M0LTE/pi-transceiver/electronics/bits'n_bobs/Modular_PA Controller/HF PA Radio Interface/RaspberryPi_Pico/README.txt

**A comprehensive KiCad Library for the Raspberry Pi Pico** 🥧
==============================================================

### Providing footprints, symbols, & models for the module's various forms & implementations

> *This git submodule only contains the finished library.  For source files and commit history, see [Ki-Lime Pi Pico][URL-Repository]*.

***Features***
==============

- **KiCad 8.0 support** *(For KiCad 7.0 support, checkout tag `1.1.0`)*
- **Schematics with alternate pin definitions** to select more specific behaviours for each GPIO, as well as specify power directionality
- **Generic and specific footprints** for the Pico and Pico W
  - Through-hole and surface-mount footprints with and without mounting holes
  - Hand-solderable test points (ie. USB signals) in footprints with underside castellations
  - Optional pin labels as an add-on footprint
  - Optional keepout zone for 2.4 GHz RF on shared footprints
  - Ability to add individual schematic symbols for sockets, and a virtual Pico for the BOM and rendering
- **Diverse 3D models** for surface-mount, through-hole, and socketed forms of the Pico, Pico H, Pico W, and Pico WH using photorealistic materials
- Majority adherence to the [KiCad Library Conventions][URL-KLC] version 3.0.41

***How do I use this library as a git submodule?***
===================================================

> *If you're looking to use this library without submodules, you probably want the source repository [Ki-Lime Pi Pico][URL-Repository].*

- Ensure you are running KiCad 7.0 or later
- Identify the path where you want this library to live in your project  
  *(below, I will use `<GIT-ROOT>/pcb/project-libraries/RaspberryPi_Pico`)*
- From within your git repository, call:
  - `git submodule add --name ki-lime-pi-pico https://github.com/recursivenomad/ki-lime-pi-to-go.git pcb/project-libraries/RaspberryPi_Pico`  
    *(Adjusting these parameters as you see fit)*
  - `cd pcb/project-libraries/RaspberryPi_Pico`
  - `git checkout 2.0.0` *(For KiCad 7.0 support, checkout `1.1.0` instead)*
- Open the relevant KiCad project
- Select `Preferences > Manage Footprint Libraries...`
- Select the `Project Specific Libraries` tab
- Click the folder icon in the lower left to `Add Existing`
- Navigate to and select `.../RaspberryPi_Pico/Module_RaspberryPi_Pico.pretty/`
- Click `OK`
- Select `Preferences > Manage Symbol Libraries...`
- Select the `Project Specific Libraries` tab
- Click the folder icon in the lower left to `Add existing library to table`
- Navigate to and select `.../RaspberryPi_Pico/MCU_Module_RaspberryPi_Pico.kicad_sym`
- Click `OK`

To use, simply add a symbol to your schematic as you would any other; symbols should be located under the section `MCU_Module_RaspberryPi_Pico`, and footprints under `Module_RaspberryPi_Pico`.

**You're all set to design exciting new circuit boards using the Raspberry Pi Pico! 🎉**

***Further reading***
=====================

*Further reading available in the [source repository][URL-Repository].*

***License / Access***
======================

This work is made freely available under the [*MIT-0*][URL-MIT-0] license, rendered in [`LICENSE.txt`](./LICENSE.txt).  
Although attribution is not required, sharing when you've made something with my work is really cool ❤✨

*No additional/conflicting permissions were present in this repository at the time of release.*

----------------------

*Repository: <https://gitlab.com/recursivenomad/ki-lime-pi-pico/>*  
*Releases: <https://gitlab.com/recursivenomad/ki-lime-pi-pico/-/releases/>*  
*Submodule: <https://github.com/recursivenomad/ki-lime-pi-to-go/>*  
*Contact: <recursivenomad@protonmail.com>*

----------------------

### Donations:

*Accepted, but not expected*

> Online payment: <https://donate.stripe.com/dR6dSU1PueevgKY4gs>

> Monero (XMR): `8Bhyeo232EVDiK7aRSzHGRC28RZ1H6FL55V6CVyCVtxdDRQXHk8btPU8Wr5G8K3AWgaK19JfYbshKfHWqc177jwtCtCSaz1`

> Ether (ETH): `0xD1b824f2Ec3D609e816B04A301124129602A5238`

> Bitcoin (BTC): `bc1qadq5kyuuc7etgu5ywlygnaepqhzgc2u7gxkze2`

[URL-MIT-0]: <https://opensource.org/license/mit-0/>

[URL-Repository]: <https://gitlab.com/recursivenomad/ki-lime-pi-pico/>

[URL-KiCad-Forums-cdwilson]: <https://forum.kicad.info/t/21104>
[URL-KiCad-Forums-mgyger]: <https://forum.kicad.info/t/35844/12>
[URL-KLC]: <https://klc.kicad.org/>
[URL-Official-Example]: <https://datasheets.raspberrypi.com/rp2040/hardware-design-with-rp2040.pdf#page=15>
