M0LTE/pi-transceiver/electronics/PSU Board/Schematic.png

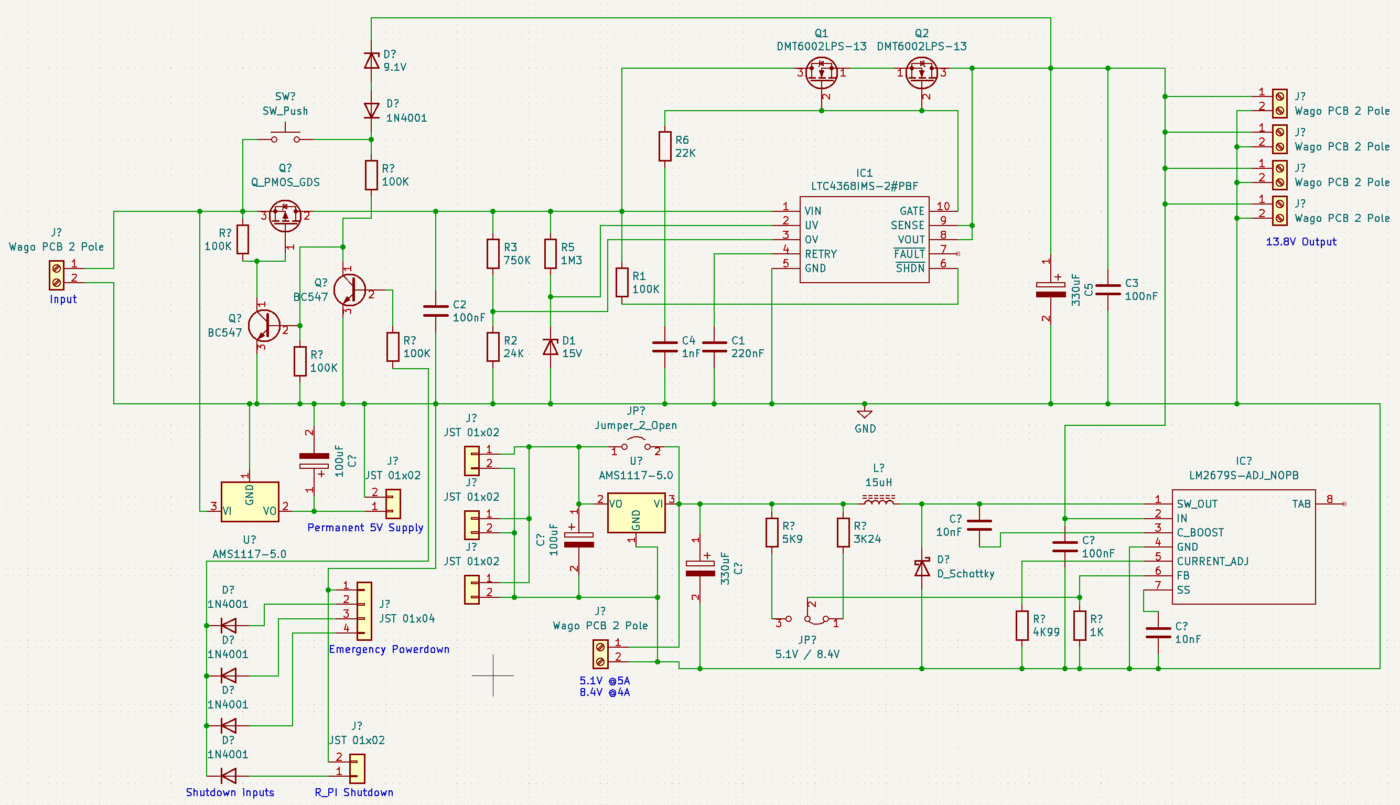
electronics/PSU Board/Schematic.png
