M0LTE/pi-transceiver/electronics/PSU Board/WEBENCH LM2679 Efficiency.png

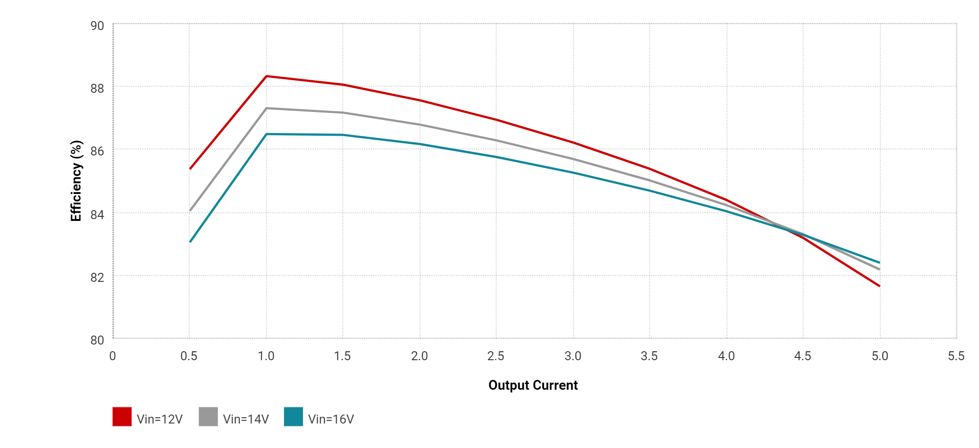
electronics/PSU Board/WEBENCH LM2679 Efficiency.png
