M0LTE/pi-transceiver/electronics/PSU Board/WEBENCH LM2679 Schematic.png

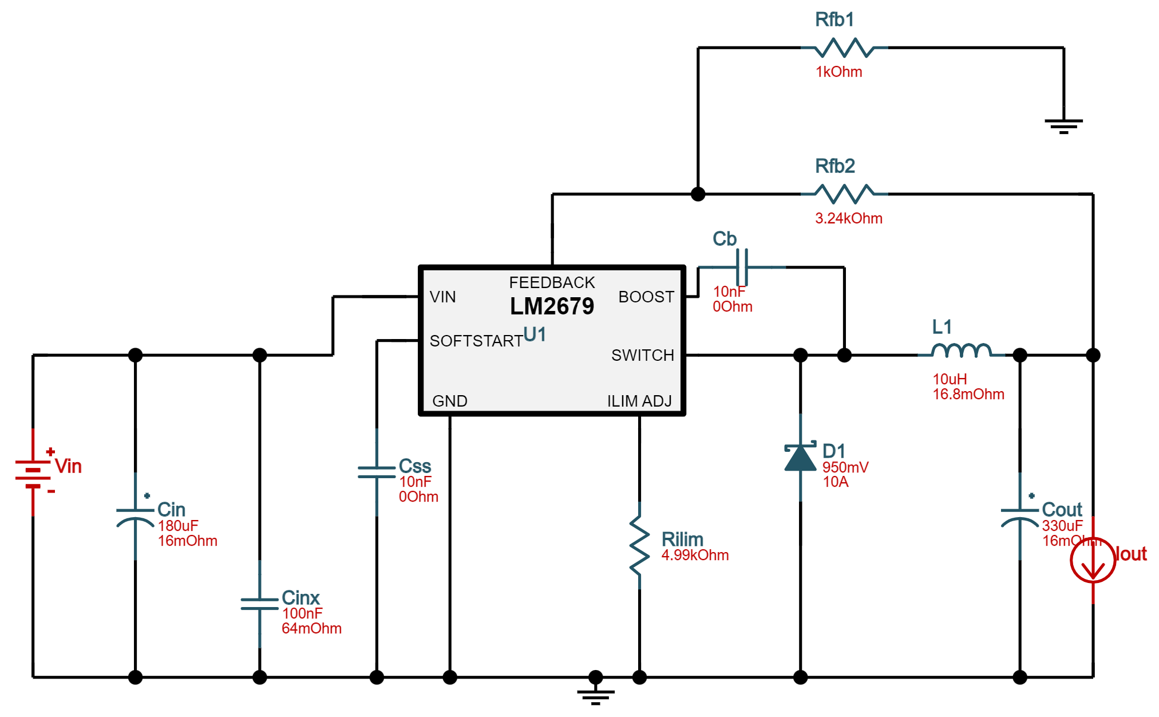
electronics/PSU Board/WEBENCH LM2679 Schematic.png
