M0LTE/pi-transceiver/electronics/receiver/RXLNA.jpg

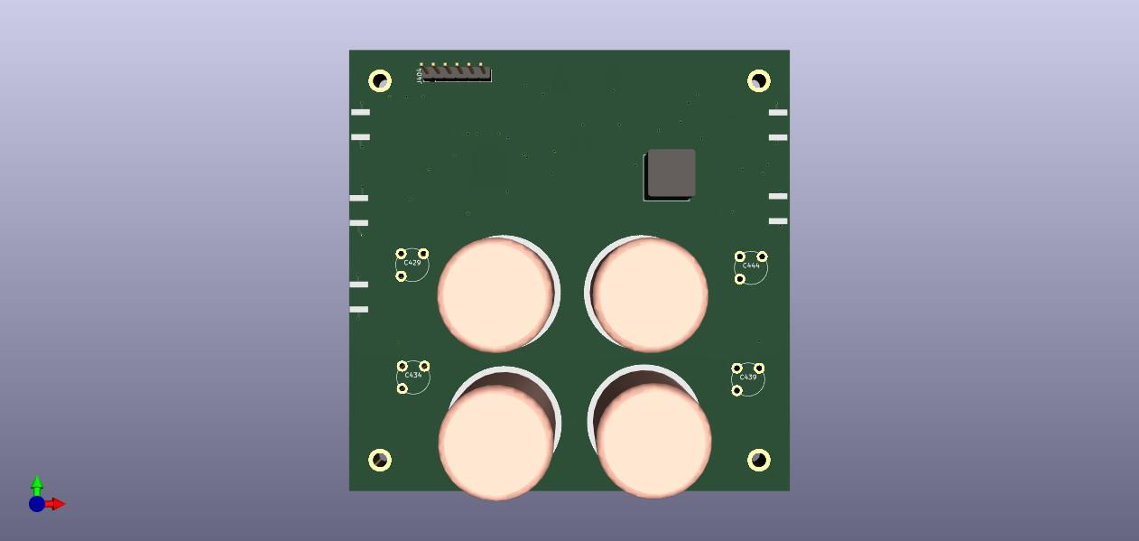
electronics/receiver/RXLNA.jpg
