M0LTE/pi-transceiver/electronics/PA_Board_V2/JST/JST_PH/JST - PH - SMD - Right - 1.25mm/JST - PH - SMD (R) - 13Pin - 2.00mm.stp

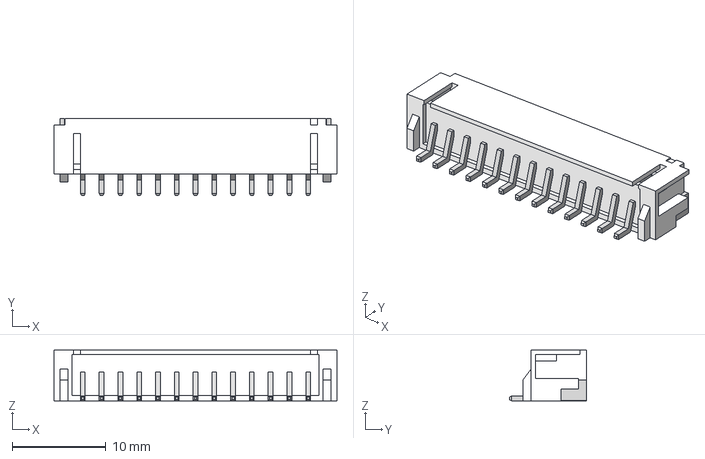
[picture p19: CAD file, 2022-10-31]
electronics/PA_Board_V2/JST/JST_PH/JST - PH - SMD - Right - 1.25mm/JST - PH - SMD (R) - 13Pin - 2.00mm.stp
30.1 x 8.26 x 5.38 mm
