M0LTE/pi-transceiver/electronics/bits'n_bobs/Modular_PA Controller/PA_Power_V1/RLab Keyboard/3D_Models/3214G.stp

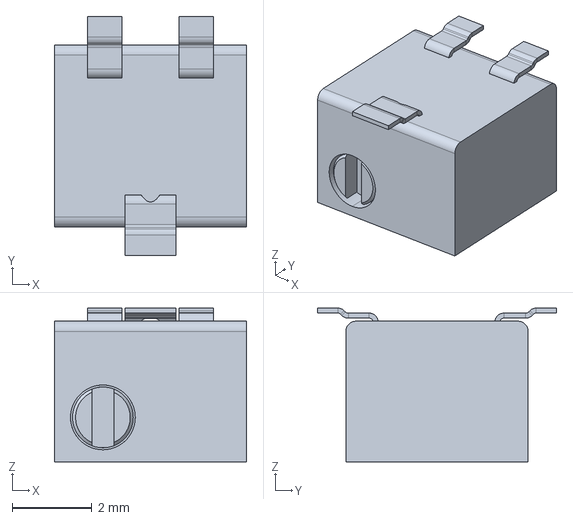
[picture p25: CAD file, 2024-11-24]
electronics/bits'n_bobs/Modular_PA Controller/PA_Power_V1/RLab Keyboard/3D_Models/3214G.stp
4.83 x 5.99 x 3.86 mm
