M0LTE/pi-transceiver/electronics/PA_Board_V2/3D/SAMTEC_RF174-01SPX-06BJX-XXX-S-1.STEP

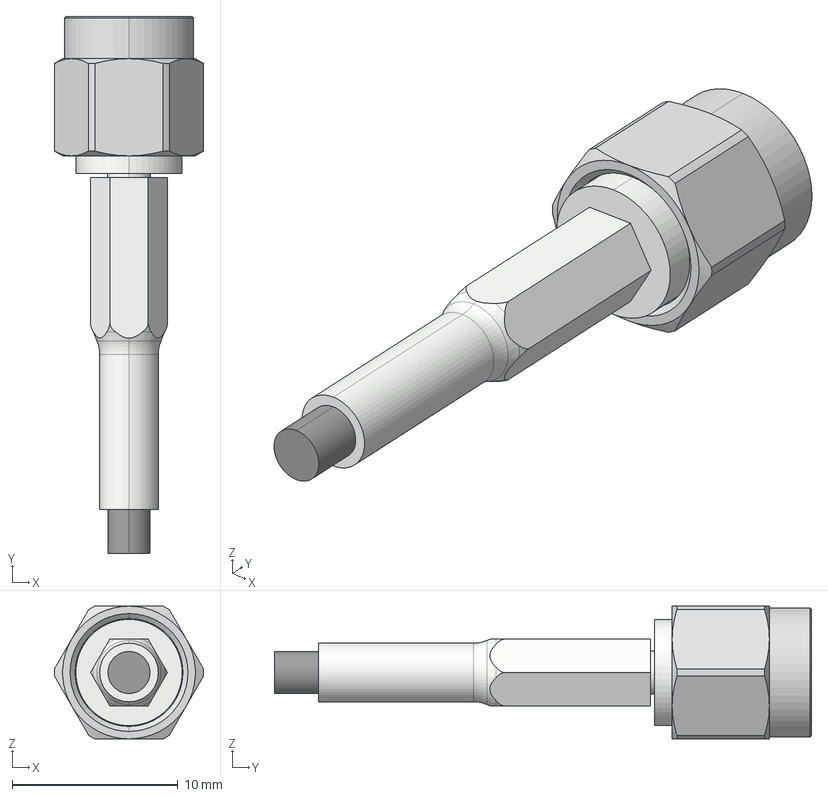
[picture p26: CAD file, 2022-10-31]
electronics/PA_Board_V2/3D/SAMTEC_RF174-01SPX-06BJX-XXX-S-1.STEP
9.00 x 32.4 x 8.00 mm
