M0LTE/pi-transceiver/electronics/PA_Board_V2/JST/JST_PH/JST - PH - Thru - Vertical - 2.00mm/JST - PH - Thru (V) - 16Pin - 2.00mm.stp

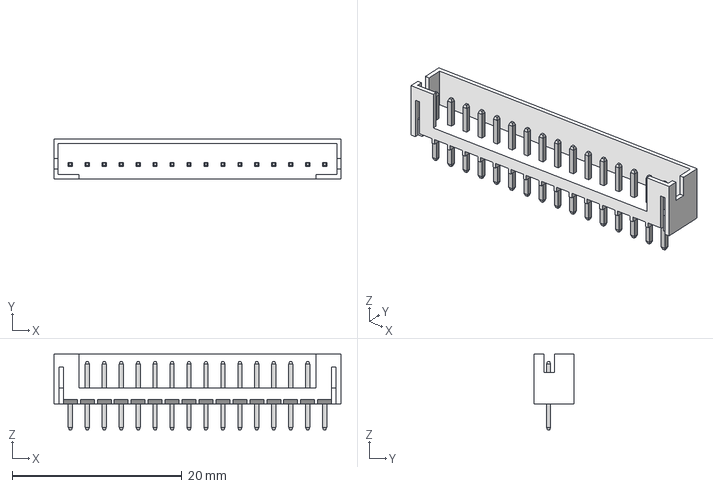
[picture p28: CAD file, 2022-10-31]
electronics/PA_Board_V2/JST/JST_PH/JST - PH - Thru - Vertical - 2.00mm/JST - PH - Thru (V) - 16Pin - 2.00mm.stp
33.9 x 4.67 x 8.94 mm
