M0LTE/pi-transceiver/electronics/PA_Board_V2/JST/JST_SH/SHR-xxV-S/SHR-10V-S.STEP

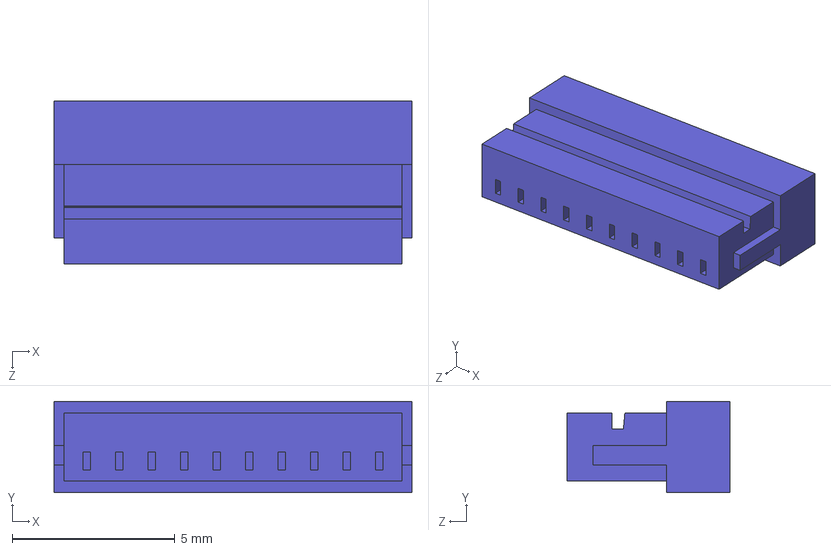
[picture p31: CAD file, 2022-10-31]
electronics/PA_Board_V2/JST/JST_SH/SHR-xxV-S/SHR-10V-S.STEP
11.0 x 2.80 x 5.00 mm
