M0LTE/pi-transceiver/electronics/bits'n_bobs/Modular_PA Controller/PA_Power_V1/RLab Keyboard/3D_Models/PJ311D_WPos.STEP

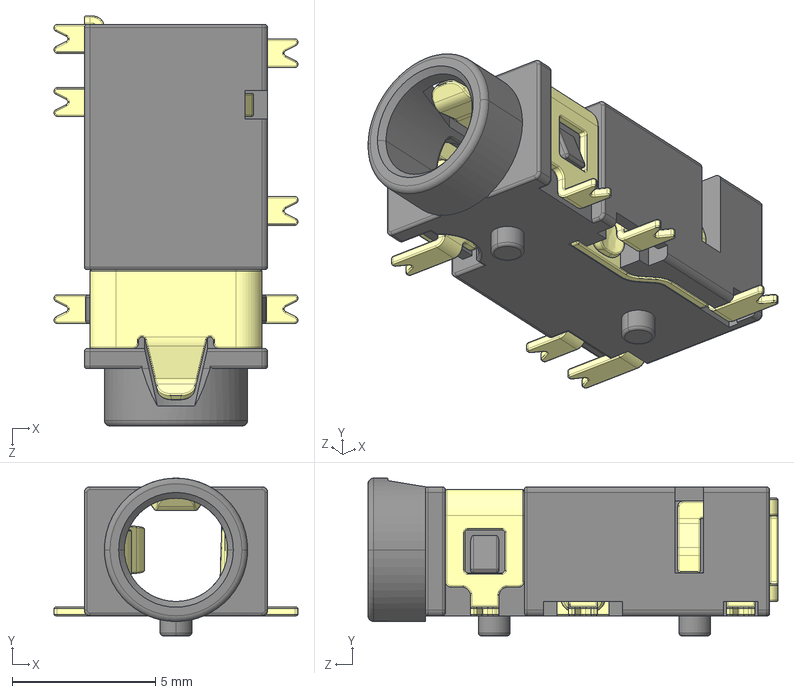
[picture p33: CAD file, 2024-11-24]
electronics/bits'n_bobs/Modular_PA Controller/PA_Power_V1/RLab Keyboard/3D_Models/PJ311D_WPos.STEP
8.50 x 5.50 x 14.3 mm
001^PJ311D_WPos
002^PJ311D_WPos
003^PJ311D_WPos
004^PJ311D_WPos
005^PJ311D_WPos
006^PJ311D_WPos
007^PJ311D_WPos
