M0LTE/pi-transceiver/electronics/PA_Board_V2/3D/Power Pole v1.step

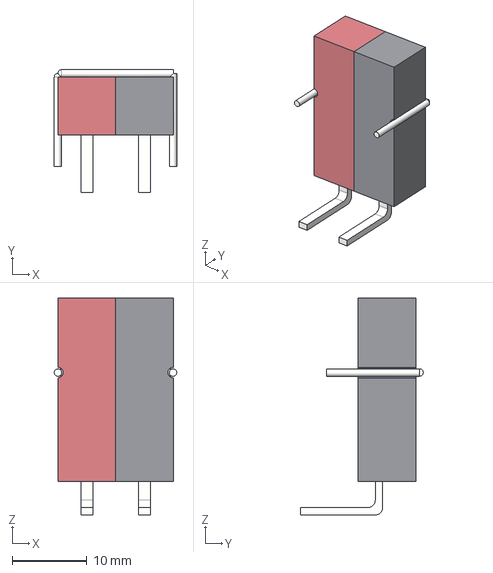
[picture p34: CAD file, 2022-10-31]
electronics/PA_Board_V2/3D/Power Pole v1.step
16.4 x 16.4 x 29.1 mm
