M0LTE/pi-transceiver/electronics/bits'n_bobs/Modular_PA Controller/PA_Power_V1/RLab Keyboard/3D_Models/1.3 TFT IPS.stp

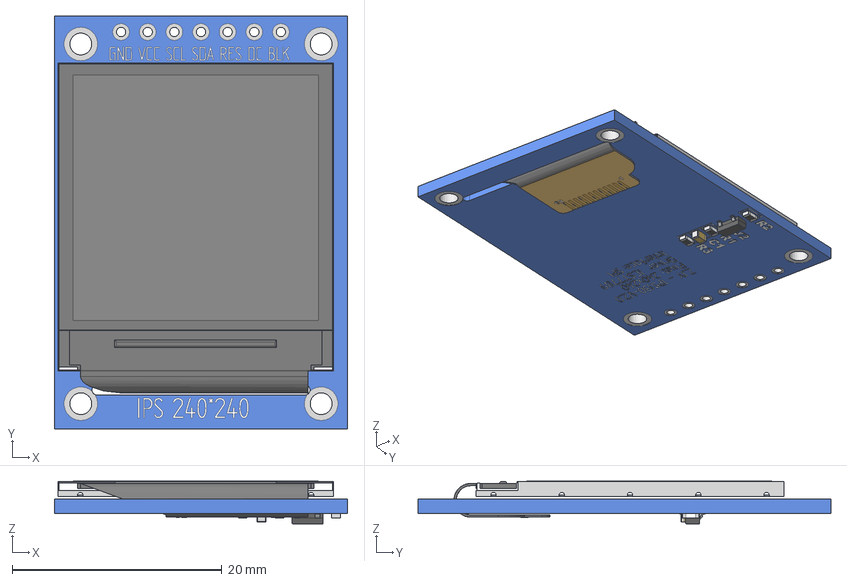
[picture p41: CAD file, 2024-11-24]
electronics/bits'n_bobs/Modular_PA Controller/PA_Power_V1/RLab Keyboard/3D_Models/1.3 TFT IPS.stp
27.9 x 39.4 x 4.06 mm
1.3 TFT IPS - Board
1.3 TFT IPS - Flush Reverse Mount
0603 Resistor x 3
0603 Capacitor
SOT-23
