M0LTE/pi-transceiver/electronics/PA_Board_V2/3D/PA_module_copper .step

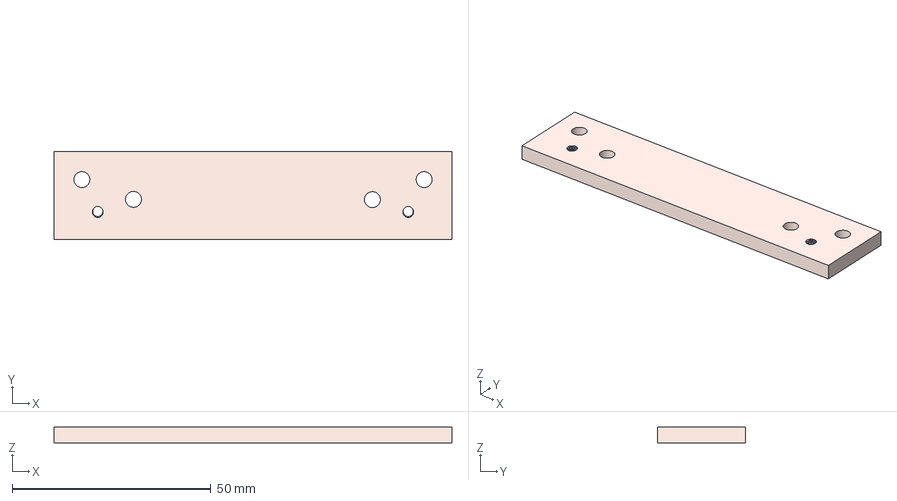
[picture p48: CAD file, 2022-10-31]
electronics/PA_Board_V2/3D/PA_module_copper .step
100.0 x 22.0 x 4.00 mm
