M0LTE/pi-transceiver/electronics/PA_Board_V2/JST/JST_SH/SHR-xxV-S/SHR-08V-S.STEP

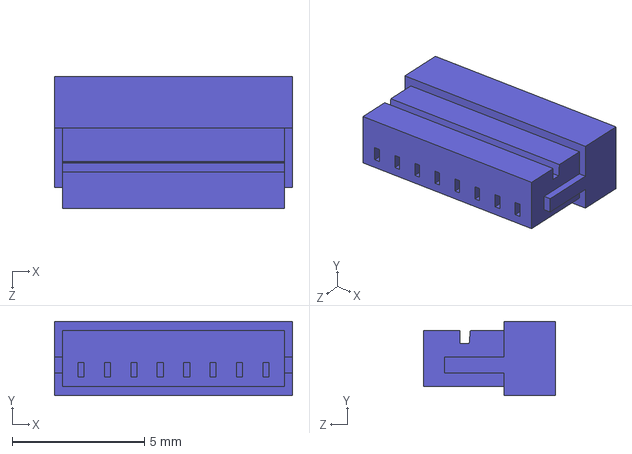
[picture p53: CAD file, 2022-10-31]
electronics/PA_Board_V2/JST/JST_SH/SHR-xxV-S/SHR-08V-S.STEP
9.00 x 2.80 x 5.00 mm
