M0LTE/pi-transceiver/electronics/PA_Board_V2/3D/SAMTEC_SMA-J-P-H-ST-EM1.STEP

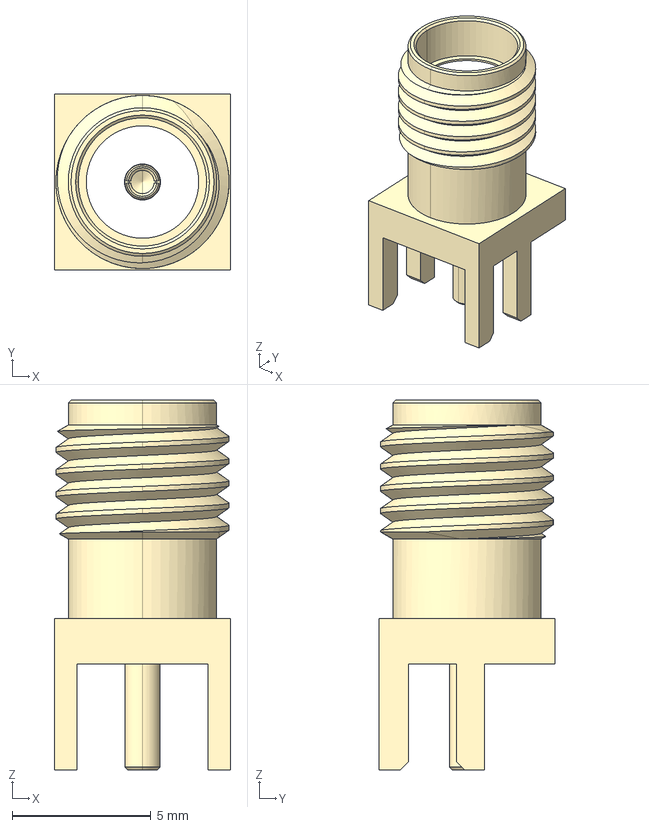
[picture p55: CAD file, 2022-10-31]
electronics/PA_Board_V2/3D/SAMTEC_SMA-J-P-H-ST-EM1.STEP
6.35 x 6.35 x 13.3 mm
