M0LTE/pi-transceiver/electronics/PA_Board_V2/3D/RF_PA_module.step

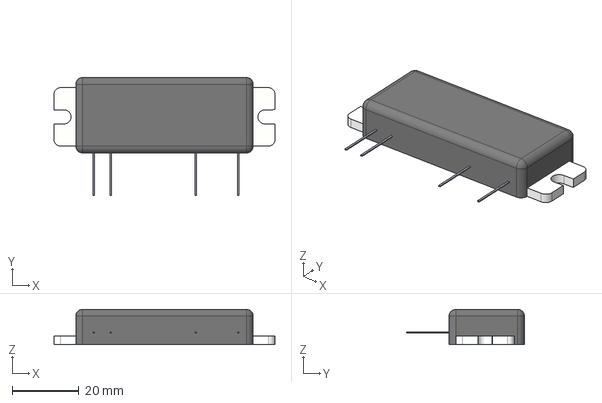
[picture p62: CAD file, 2022-10-31]
electronics/PA_Board_V2/3D/RF_PA_module.step
66.0 x 35.2 x 10.5 mm
