M0LTE/pi-transceiver/electronics/PA_Board_V2/JST/JST_SH/BMxxB-SRSR-TB/BM08B-SRSS-TB.STEP

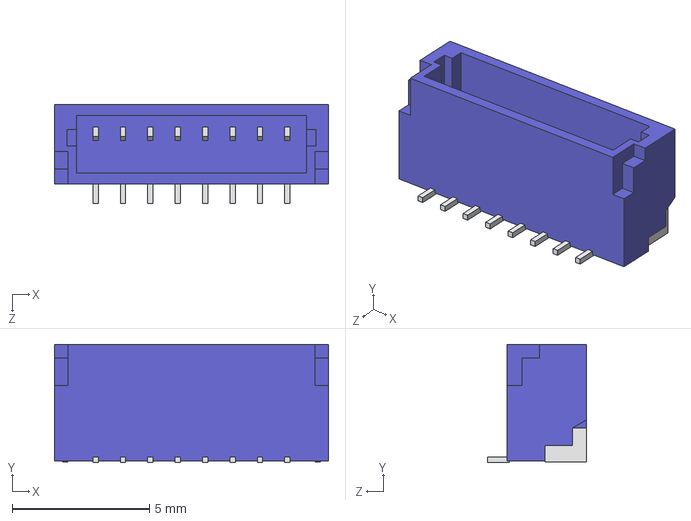
[picture p65: CAD file, 2022-10-31]
electronics/PA_Board_V2/JST/JST_SH/BMxxB-SRSR-TB/BM08B-SRSS-TB.STEP
10.0 x 4.32 x 3.60 mm
