M0LTE/pi-transceiver/electronics/PA_Board_V2/JST/JST_SH/SHR-xxV-S-B/SHR-04V-S-B.STEP

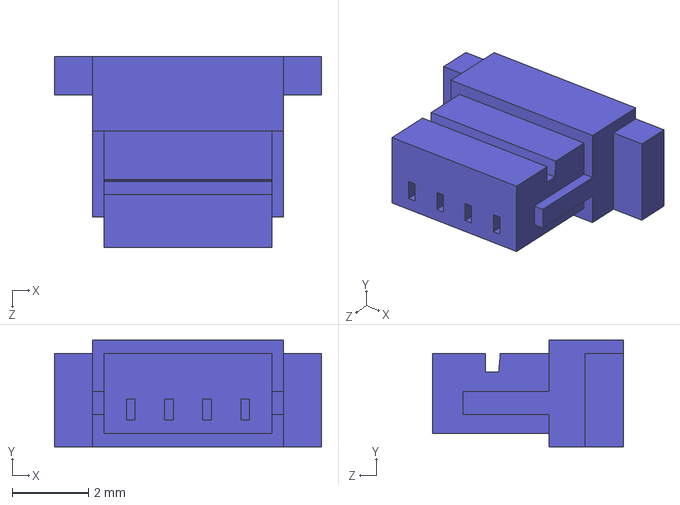
[picture p66: CAD file, 2022-10-31]
electronics/PA_Board_V2/JST/JST_SH/SHR-xxV-S-B/SHR-04V-S-B.STEP
7.00 x 2.80 x 5.00 mm
