M0LTE/pi-transceiver/electronics/PA_Board_V2/JST/JST_SH/SMxxB-SRSS-TB/SM03B-SRSS-TB.STEP

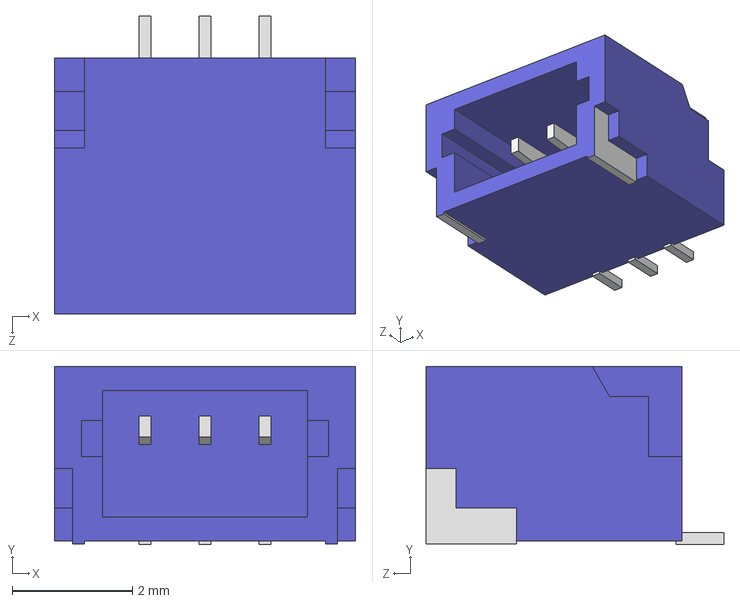
[picture p92: CAD file, 2022-10-31]
electronics/PA_Board_V2/JST/JST_SH/SMxxB-SRSS-TB/SM03B-SRSS-TB.STEP
5.00 x 2.96 x 4.95 mm
