M0LTE/pi-transceiver/electronics/PA_Board_V2/JST/JST_SH/SHR-xxV-S-B/SHR-15V-S-B.STEP

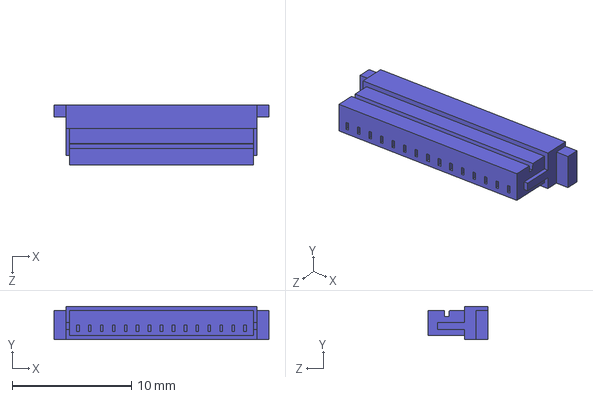
[picture p96: CAD file, 2022-10-31]
electronics/PA_Board_V2/JST/JST_SH/SHR-xxV-S-B/SHR-15V-S-B.STEP
18.0 x 2.80 x 5.00 mm
