M0LTE/pi-transceiver/electronics/PA_Board_V2/JST/JST_SH/BMxxB-SRSR-TB/BM03B-SRSS-TB.STEP

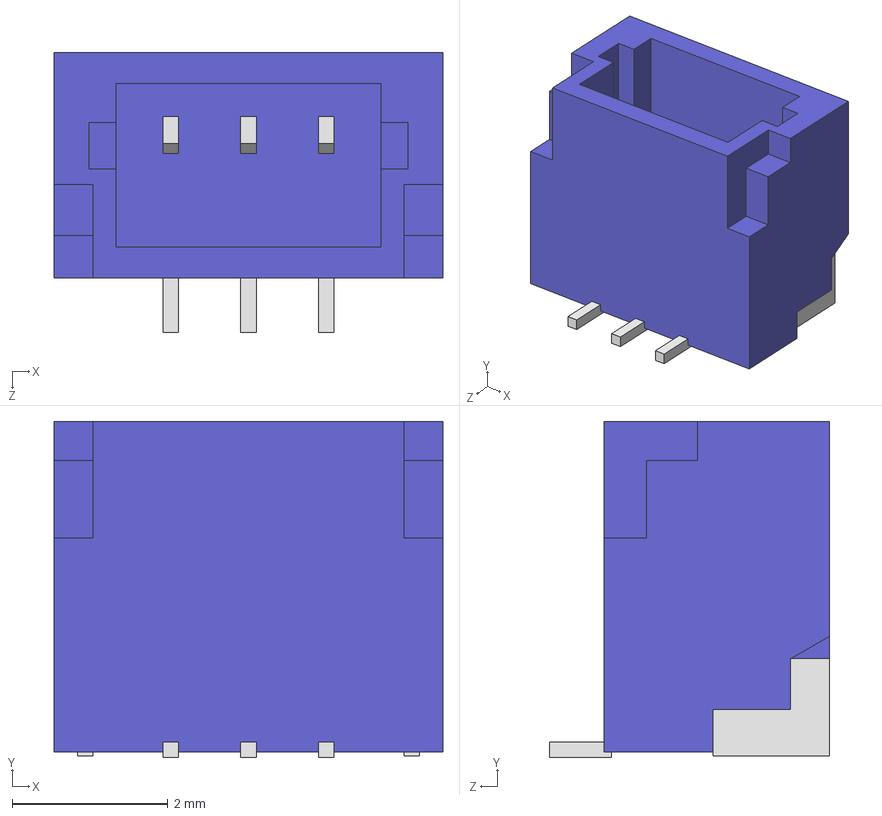
[picture p101: CAD file, 2022-10-31]
electronics/PA_Board_V2/JST/JST_SH/BMxxB-SRSR-TB/BM03B-SRSS-TB.STEP
5.00 x 4.32 x 3.60 mm
