M0LTE/pi-transceiver/electronics/PA_Board_V2/JST/JST_SH/SHR-xxV-S-B/SHR-08V-S-B.STEP

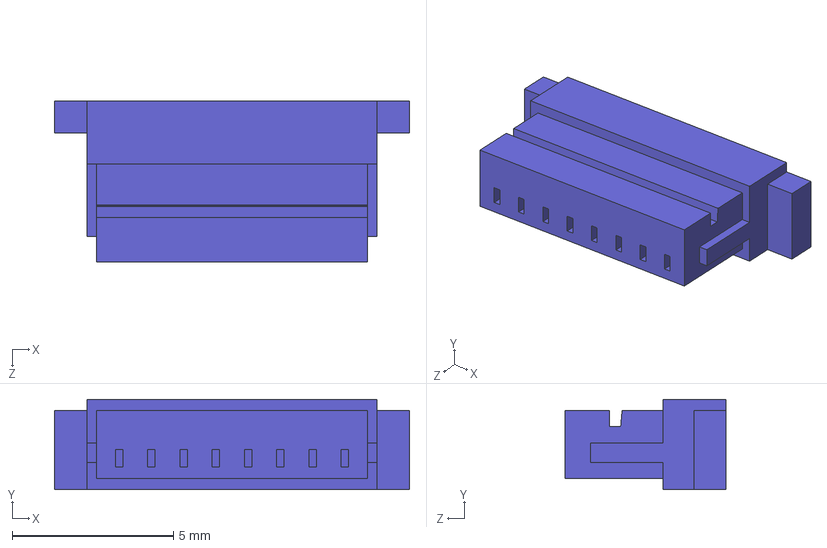
[picture p107: CAD file, 2022-10-31]
electronics/PA_Board_V2/JST/JST_SH/SHR-xxV-S-B/SHR-08V-S-B.STEP
11.0 x 2.80 x 5.00 mm
