M0LTE/pi-transceiver/electronics/bits'n_bobs/Relays/Relay_RF_HF3/Relay_RF_HF3.kicad_pcb

## KiCad design electronics/bits'n_bobs/Relays/Relay_RF_HF3/Relay_RF_HF3.kicad_pcb (2022-03-16)

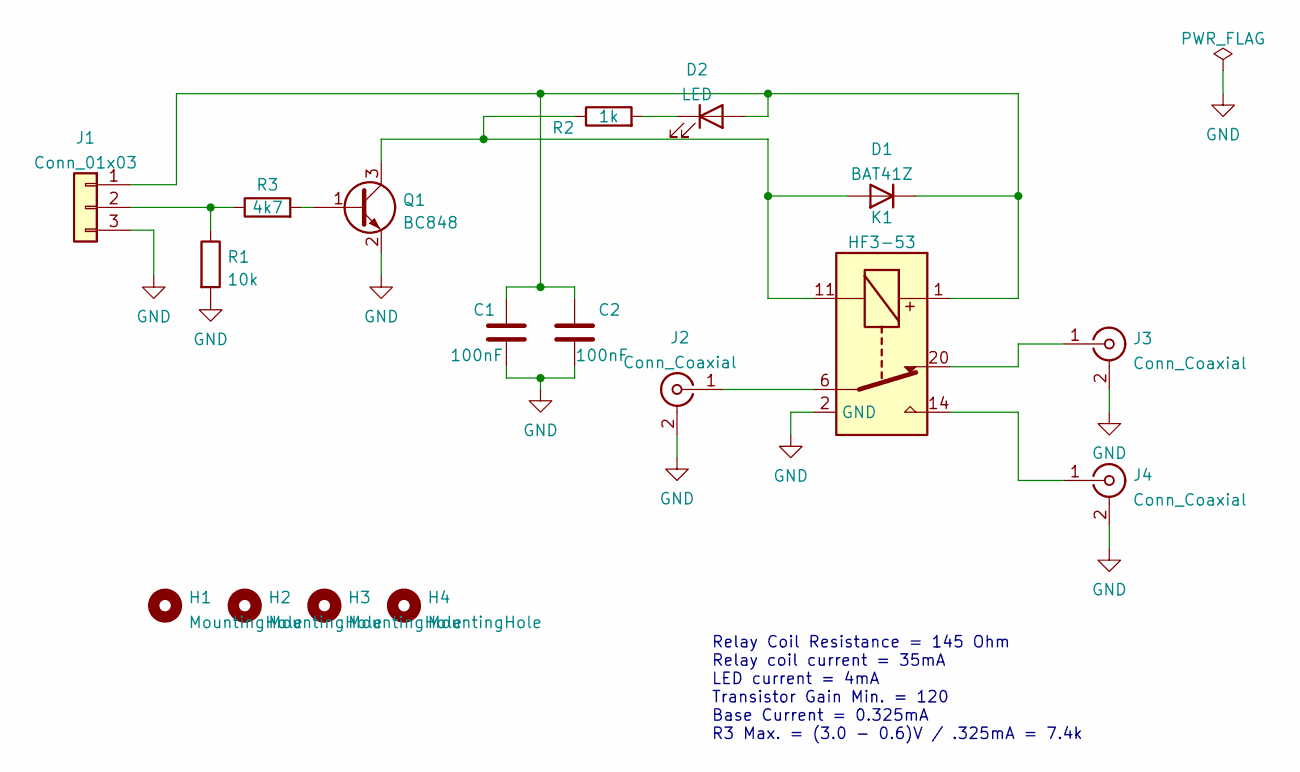
[picture p150: schematic Relay_RF_HF3.kicad_sch]

Parts:
C1, C2: 100nF; C_0603_1608Metric
D1: BAT41Z; D_SOD-123
D2: LED; LED_0603_1608Metric
H1, H2, H3, H4: MountingHole; MountingHole_2.7mm_M2.5_DIN965
J1: Conn_01x03; JST_PH_B3B-PH-SM4-TB_1x03-1MP_P2.00mm_Vertical
J2, J3, J4: Conn_Coaxial; SMA_Samtec_SMA-J-P-X-ST-EM1_EdgeMount
K1: HF3-53; Relay_SPDT_AXICOM_HF3Series_50ohms_Pitch1.27mm
Q1: BC848; SOT-23
R1: 10k; R_0603_1608Metric
R2: 1k; R_0603_1608Metric
R3: 4k7; R_0603_1608Metric

Connections:
GND: C1.2, C2.2, J1.3, J2.2 (Ext), J3.2 (Ext), J4.2 (Ext), K1.2 (GND), K1.5 (GND), K1.7 (GND), K1.10 (GND), K1.12 (GND), K1.13 (GND), K1.15 (GND), K1.17 (GND), K1.19 (GND), K1.21 (GND), K1.22 (GND), Q1.2 (E), R1.2
unnamed: C1.1, C2.1, D1.1 (K), D2.2 (A), J1.1, K1.1
unnamed: D1.2 (A), K1.11, Q1.3 (C), R2.1
unnamed: D2.1 (K), R2.2
unnamed: J1.2, R1.1, R3.1
unnamed: J2.1 (In), K1.6
unnamed: J3.1 (In), K1.20
unnamed: J4.1 (In), K1.14
unnamed: Q1.1 (B), R3.2

Notes on the sheet:
Relay Coil Resistance = 145 Ohm Relay coil current = 35mA LED current = 4mA Transistor Gain Min. = 120 Base Current = 0.325mA R3 Max. = (3.0 - 0.6)V / .325mA = 7.4k

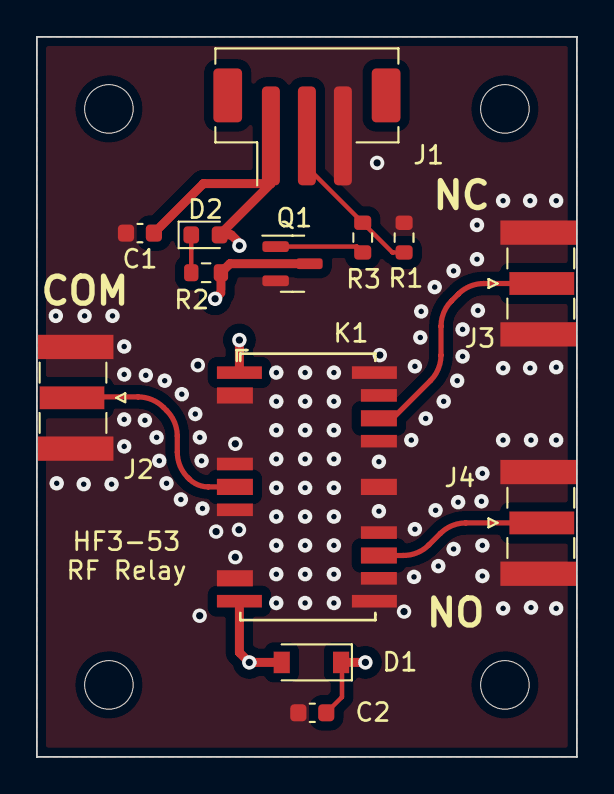
[picture p151: board Relay_RF_HF3.kicad_pcb from above]

Board: 4 copper layers, 30.0 x 40.0 mm, 17 parts (0 on the bottom side), 9 nets.
