M0LTE/pi-transceiver/electronics/bits'n_bobs/Filters/RBP-140+/RBP-140+.kicad_pcb

## KiCad design electronics/bits'n_bobs/Filters/RBP-140+/RBP-140+.kicad_pcb (2022-03-16)

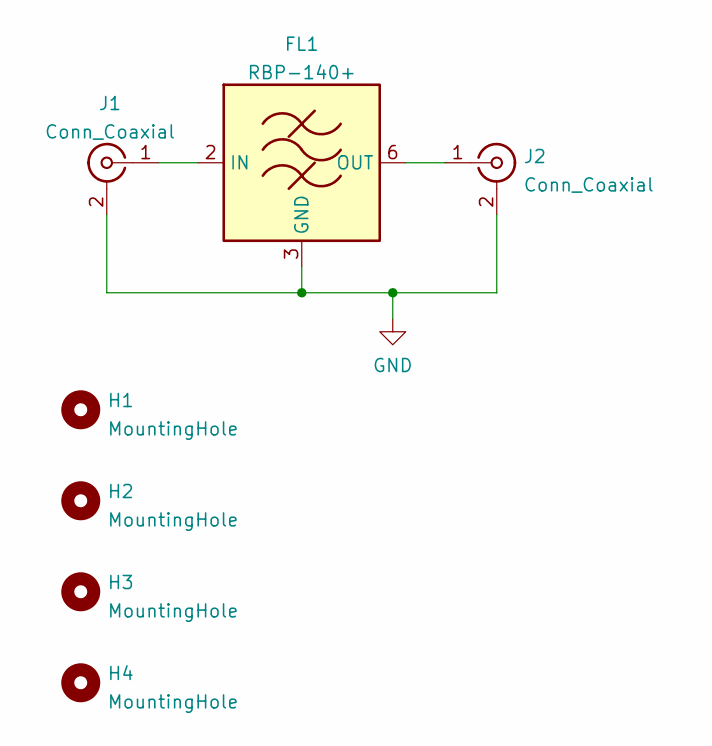
[picture p152: schematic RBP-140+.kicad_sch]

Parts:
FL1: RBP-140+; Mini-Circuits_GP731_LandPatternPL-176
H1, H2, H3, H4: MountingHole; MountingHole_2.2mm_M2_DIN965
J1, J2: Conn_Coaxial; SMA_Samtec_SMA-J-P-X-ST-EM1_EdgeMount

Connections:
GND: FL1.1 (GND), FL1.3 (GND), FL1.4 (GND), FL1.5 (GND), FL1.7 (GND), FL1.8 (GND), J1.2 (Ext), J2.2 (Ext)
unnamed: FL1.2 (IN), J1.1 (In)
unnamed: FL1.6 (OUT), J2.1 (In)

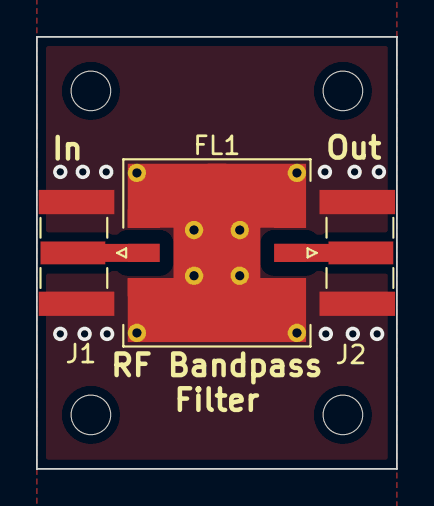
[picture p153: board RBP-140+.kicad_pcb from above]

Board: 2 copper layers, 20.0 x 24.0 mm, 7 parts (0 on the bottom side), 3 nets.
