M0LTE/pi-transceiver/electronics/bits'n_bobs/Relays/Relay_RF_G2RL/Relay_RF_G2RL.kicad_pcb

## KiCad design electronics/bits'n_bobs/Relays/Relay_RF_G2RL/Relay_RF_G2RL.kicad_pcb (2022-03-16)

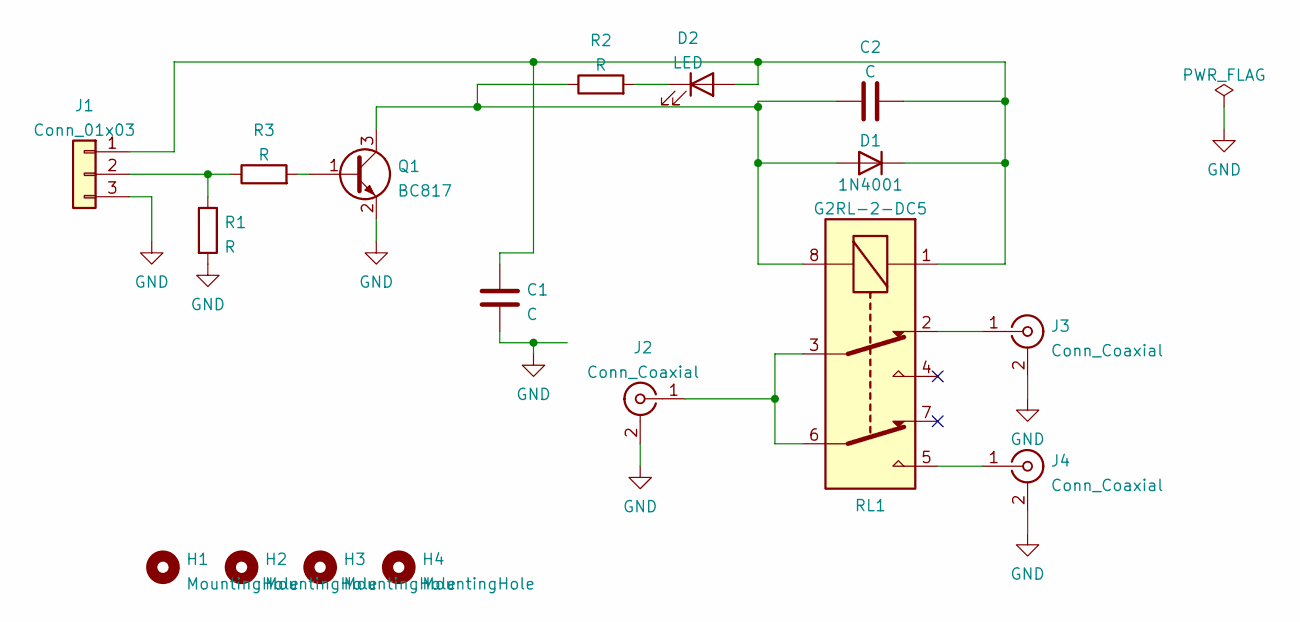
[picture p154: schematic Relay_RF_G2RL.kicad_sch]

Parts:
C1, C2: C; C_0603_1608Metric
D1: 1N4001; D_SOD-123
D2: LED; LED_0603_1608Metric
H1, H2, H3, H4: MountingHole; MountingHole_2.7mm_M2.5_DIN965
J1: Conn_01x03; JST_PH_B3B-PH-SM4-TB_1x03-1MP_P2.00mm_Vertical
J2, J3, J4: Conn_Coaxial; SMA_Samtec_SMA-J-P-X-ST-EM1_EdgeMount
Q1: BC817; SOT-23
R1, R2, R3: R; R_0603_1608Metric
RL1: G2RL-2-DC5; Relay_DPDT_Omron_G2RL

Connections:
GND: C1.2, J1.3, J2.2 (Ext), J3.2 (Ext), J4.2 (Ext), Q1.2 (E), R1.2
unnamed: C1.1, C2.2, D1.1 (K), D2.2 (A), J1.1, RL1.1
unnamed: C2.1, D1.2 (A), Q1.3 (C), R2.1, RL1.8
unnamed: D2.1 (K), R2.2
unnamed: J1.2, R1.1, R3.1
unnamed: J2.1 (In), RL1.3, RL1.6
unnamed: J3.1 (In), RL1.2
unnamed: J4.1 (In), RL1.5
unnamed: Q1.1 (B), R3.2

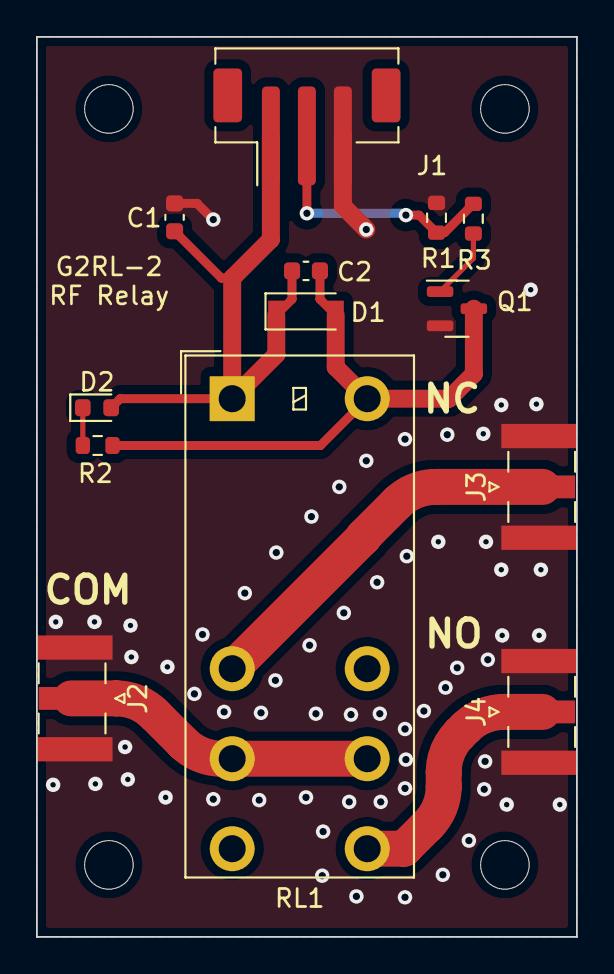
[picture p155: board Relay_RF_G2RL.kicad_pcb from above]

Board: 2 copper layers, 30.0 x 50.0 mm, 17 parts (0 on the bottom side), 9 nets.
