M0LTE/pi-transceiver/electronics/bits'n_bobs/Filters/Broadcast_Filter/Broadcast_Filter.kicad_pcb

## KiCad design electronics/bits'n_bobs/Filters/Broadcast_Filter/Broadcast_Filter.kicad_pcb (2022-03-16)

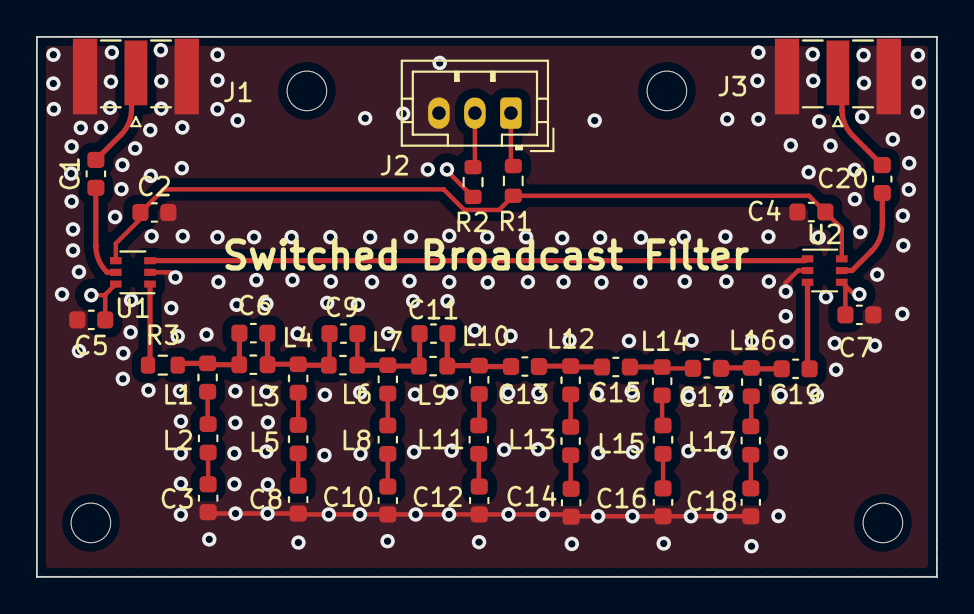
[picture p156: board Broadcast_Filter.kicad_pcb from above]

Board: 4 copper layers, 50.0 x 30.0 mm, 49 parts (0 on the bottom side), 33 nets.

Parts:
C1, C2, C3, C4, C5, C6, C7, C8, C9, C10, C11, C12, C13, C14, C15, C16, C17, C18, C19, C20: C; C_0603_1608Metric
H1, H2, H3, H4: MountingHole; MountingHole_2.2mm_M2_DIN965
J1, J3: Conn_Coaxial; SMA_Samtec_SMA-J-P-X-ST-EM1_EdgeMount
J2: Conn_01x03; JST_PH_B3B-PH-K_1x03_P2.00mm_Vertical
L1, L2, L3, L4, L5, L6, L7, L8, L9, L10, L11, L12, L13, L14, L15, L16, L17: L; L_0603_1608Metric
R1, R2, R3: R; R_0603_1608Metric
U1, U2: AS179-92LF; SOT-363_SC-70-6

Connections:
/Fil: C2.1, C4.1, R1.1, U1.4 (V1), U2.6 (V2)
/Thru: C5.1, C7.1, R2.1, U1.6 (V2), U2.4 (V1)
GND: C2.2, C3.1, C4.2, C5.2, C7.2, C8.1, C10.1, C12.1, C14.1, C16.1, C18.1, J1.2 (Ext), J2.3, J3.2 (Ext), U1.2 (GND), U2.2 (GND)
unnamed: C1.1, U1.5 (J1)
unnamed: C1.2, J1.1 (In)
unnamed: C3.2, L2.2
unnamed: C6.1, C9.2, L3.2, L4.1, L6.1
unnamed: C6.2, L1.1, L3.1, R3.1
unnamed: C8.2, L5.2
unnamed: C10.2, L8.2
unnamed: C11.1, C13.2, L9.2, L10.1
unnamed: C9.1, C11.2, L6.2, L7.1, L9.1
unnamed: C12.2, L11.2
unnamed: C13.1, C15.2, L12.1
unnamed: C14.2, L13.2
unnamed: C15.1, C17.2, L14.1
unnamed: C16.2, L15.2
unnamed: C17.1, C19.2, L16.1
unnamed: C18.2, L17.2
unnamed: C19.1, U2.3 (J2)
unnamed: C20.1, J3.1 (In)
unnamed: C20.2, U2.5 (J1)
unnamed: J2.1, R1.2
unnamed: J2.2, R2.2
unnamed: L1.2, L2.1
unnamed: L4.2, L5.1
unnamed: L7.2, L8.1
unnamed: L10.2, L11.1
unnamed: L12.2, L13.1
unnamed: L14.2, L15.1
unnamed: L16.2, L17.1
unnamed: R3.2, U1.1 (J3)
unnamed: U1.3 (J2), U2.1 (J3)
