M0LTE/pi-transceiver/electronics/bits'n_bobs/Filters/LowPass_7mm/LowPass_7mm.kicad_pcb

## KiCad design electronics/bits'n_bobs/Filters/LowPass_7mm/LowPass_7mm.kicad_pcb (2022-03-16)

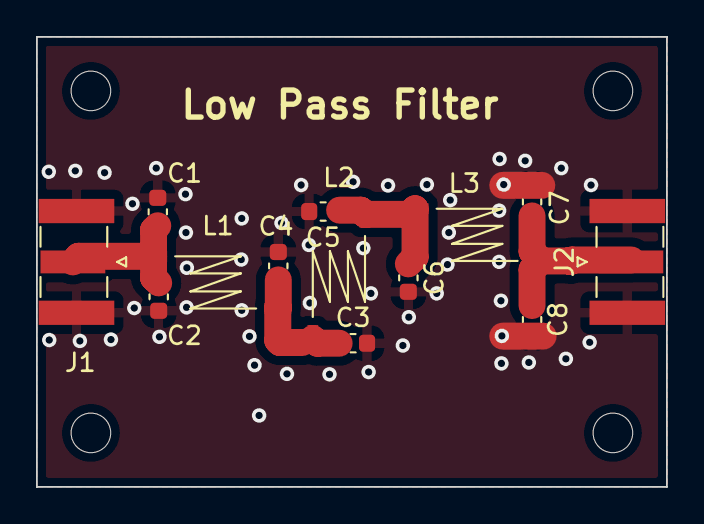
[picture p157: board LowPass_7mm.kicad_pcb from above]

Board: 2 copper layers, 35.0 x 25.0 mm, 17 parts (0 on the bottom side), 5 nets.

Parts:
C1, C2, C3, C4, C5, C6, C7, C8: C; C_0603_1608Metric
H1, H2, H3, H4: MountingHole; MountingHole_2.2mm_M2_DIN965
J1, J2: Conn_Coaxial; SMA_Samtec_SMA-J-P-X-ST-EM1_EdgeMount
L1, L2, L3: L; L_Neosid_Air-Coil_SML_3turn_HDM0331A

Connections:
GND: C1.2, C2.2, C3.2, C4.2, C5.2, C6.2, C7.2, C8.2, J1.2 (Ext), J2.2 (Ext)
unnamed: C1.1, C2.1, J1.1 (In), L1.1
unnamed: C3.1, C4.1, L1.2, L2.1
unnamed: C5.1, C6.1, L2.2, L3.1
unnamed: C7.1, C8.1, J2.1 (In), L3.2
