M0LTE/pi-transceiver/electronics/bits'n_bobs/Attenuators/PE4302/PE4302.kicad_pcb

## KiCad design electronics/bits'n_bobs/Attenuators/PE4302/PE4302.kicad_pcb (2022-03-16)

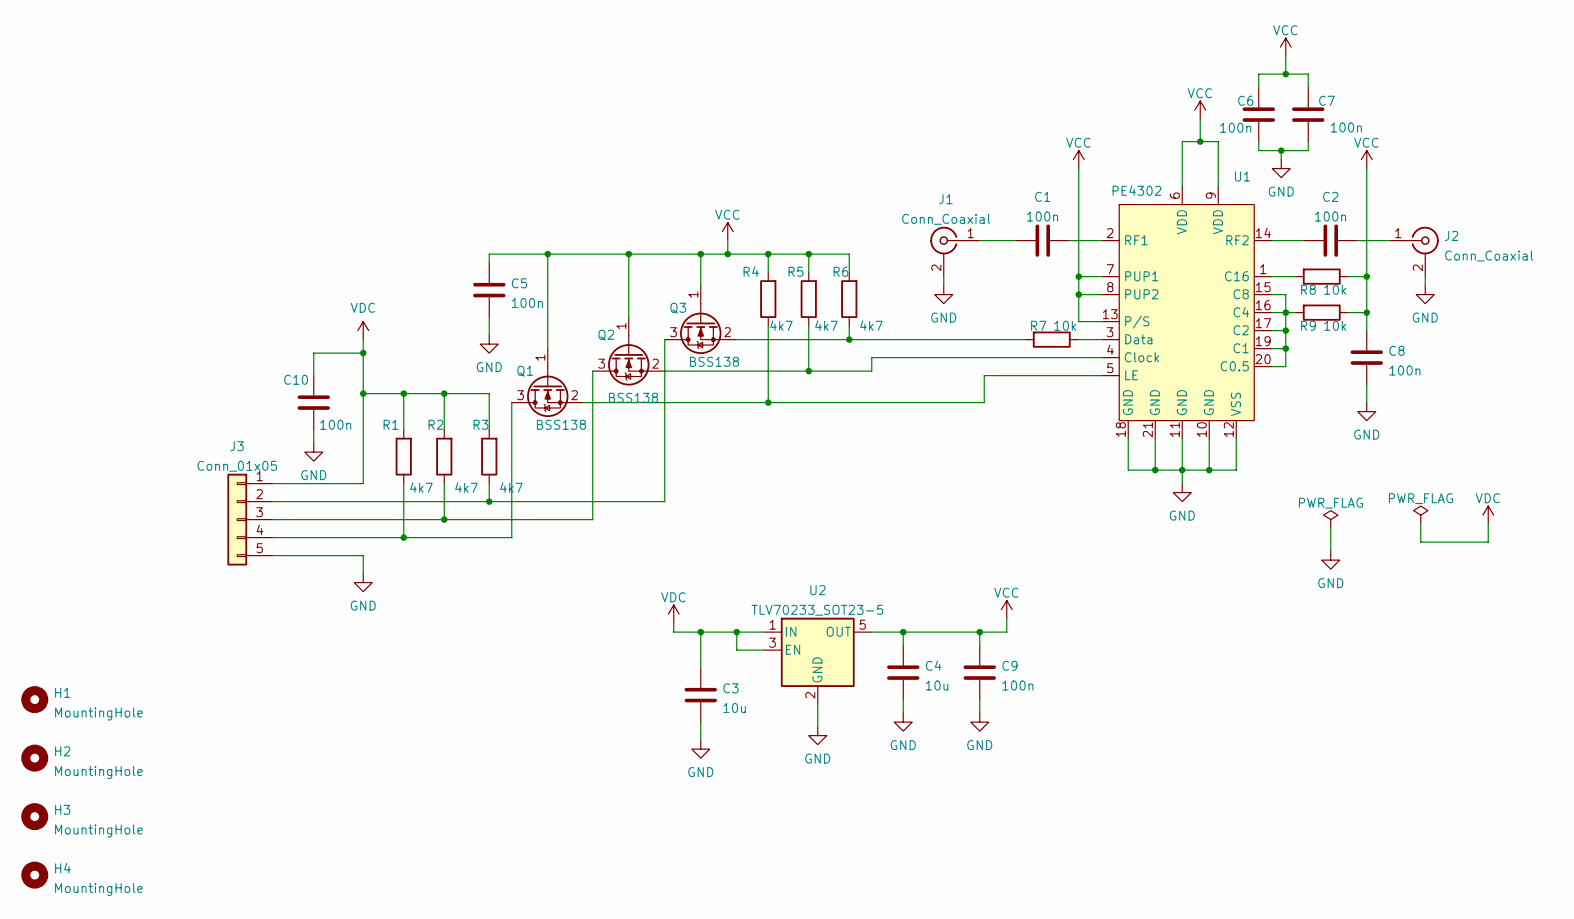
[picture p158: schematic PE4302.kicad_sch]

Parts:
C1, C2, C5, C6, C7, C8, C9, C10: 100n; C_0603_1608Metric
C3, C4: 10u; C_0805_2012Metric
H1, H2, H3, H4: MountingHole; MountingHole_2.2mm_M2
J1, J2: Conn_Coaxial; SMA_Samtec_SMA-J-P-X-ST-EM1_EdgeMount
J3: Conn_01x05; JST_PH_B5B-PH-K_1x05_P2.00mm_Vertical
Q1, Q2, Q3: BSS138; SOT-23
R1, R2, R3, R4, R5, R6: 4k7; R_0603_1608Metric
R7, R8, R9: 10k; R_0603_1608Metric
U1: PE4302; QFN-20-1EP_4x4mm_P0.5mm_EP2x2mm
U2: TLV70233_SOT23-5; SOT-23-5

Connections:
GND: C3.1, C4.1, C5.2, C6.2, C7.2, C8.2, C9.1, C10.2, J1.2 (Ext), J2.2 (Ext), J3.5, U1.10 (GND), U1.11 (GND), U1.12 (VSS), U1.18 (GND), U1.21 (GND), U2.2 (GND)
unnamed: C1.1, U1.2 (RF1)
unnamed: C1.2, J1.1 (In)
unnamed: C2.1, J2.1 (In)
unnamed: C2.2, U1.14 (RF2)
unnamed: J3.2, Q3.3 (D), R3.1
unnamed: J3.3, Q2.3 (D), R2.1
unnamed: J3.4, Q1.3 (D), R1.1
unnamed: Q1.2 (S), R4.1, U1.5 (LE)
unnamed: Q2.2 (S), R5.1, U1.4 (Clock)
unnamed: Q3.2 (S), R6.1, R7.2
unnamed: R7.1, U1.3 (Data)
unnamed: R8.2, U1.1 (C16)
unnamed: R9.2, U1.15 (C8), U1.16 (C4), U1.17 (C2), U1.19 (C1), U1.20 (C0.5)
VCC: C4.2, C5.1, C6.1, C7.1, C8.1, C9.2, Q1.1 (G), Q2.1 (G), Q3.1 (G), R4.2, R5.2, R6.2, R8.1, R9.1, U1.6 (VDD), U1.7 (PUP1), U1.8 (PUP2), U1.9 (VDD), U1.13 (P/S), U2.5 (OUT)
VDC: C3.2, C10.1, J3.1, R1.2, R2.2, R3.2, U2.1 (IN), U2.3 (EN)

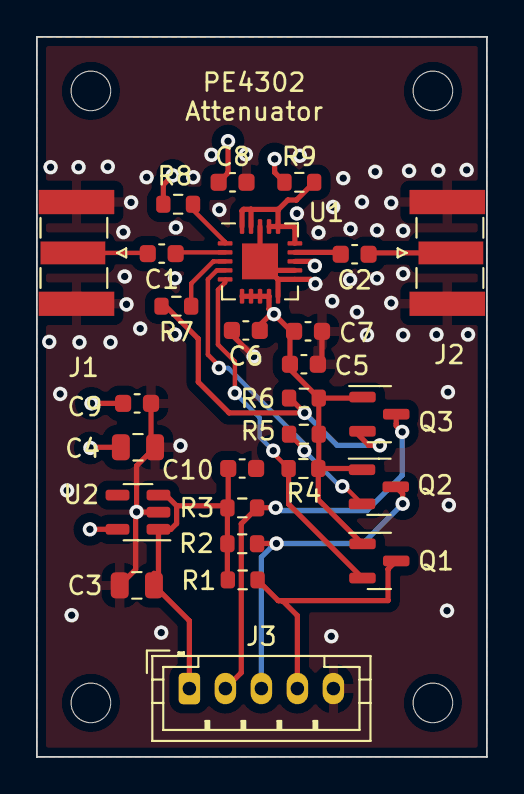
[picture p159: board PE4302.kicad_pcb from above]

Board: 4 copper layers, 25.0 x 40.0 mm, 31 parts (0 on the bottom side), 16 nets.
