M0LTE/pi-transceiver/electronics/bits'n_bobs/Couplers/Coupler/Coupler.kicad_pcb

## KiCad design electronics/bits'n_bobs/Couplers/Coupler/Coupler.kicad_pcb (2022-03-16)

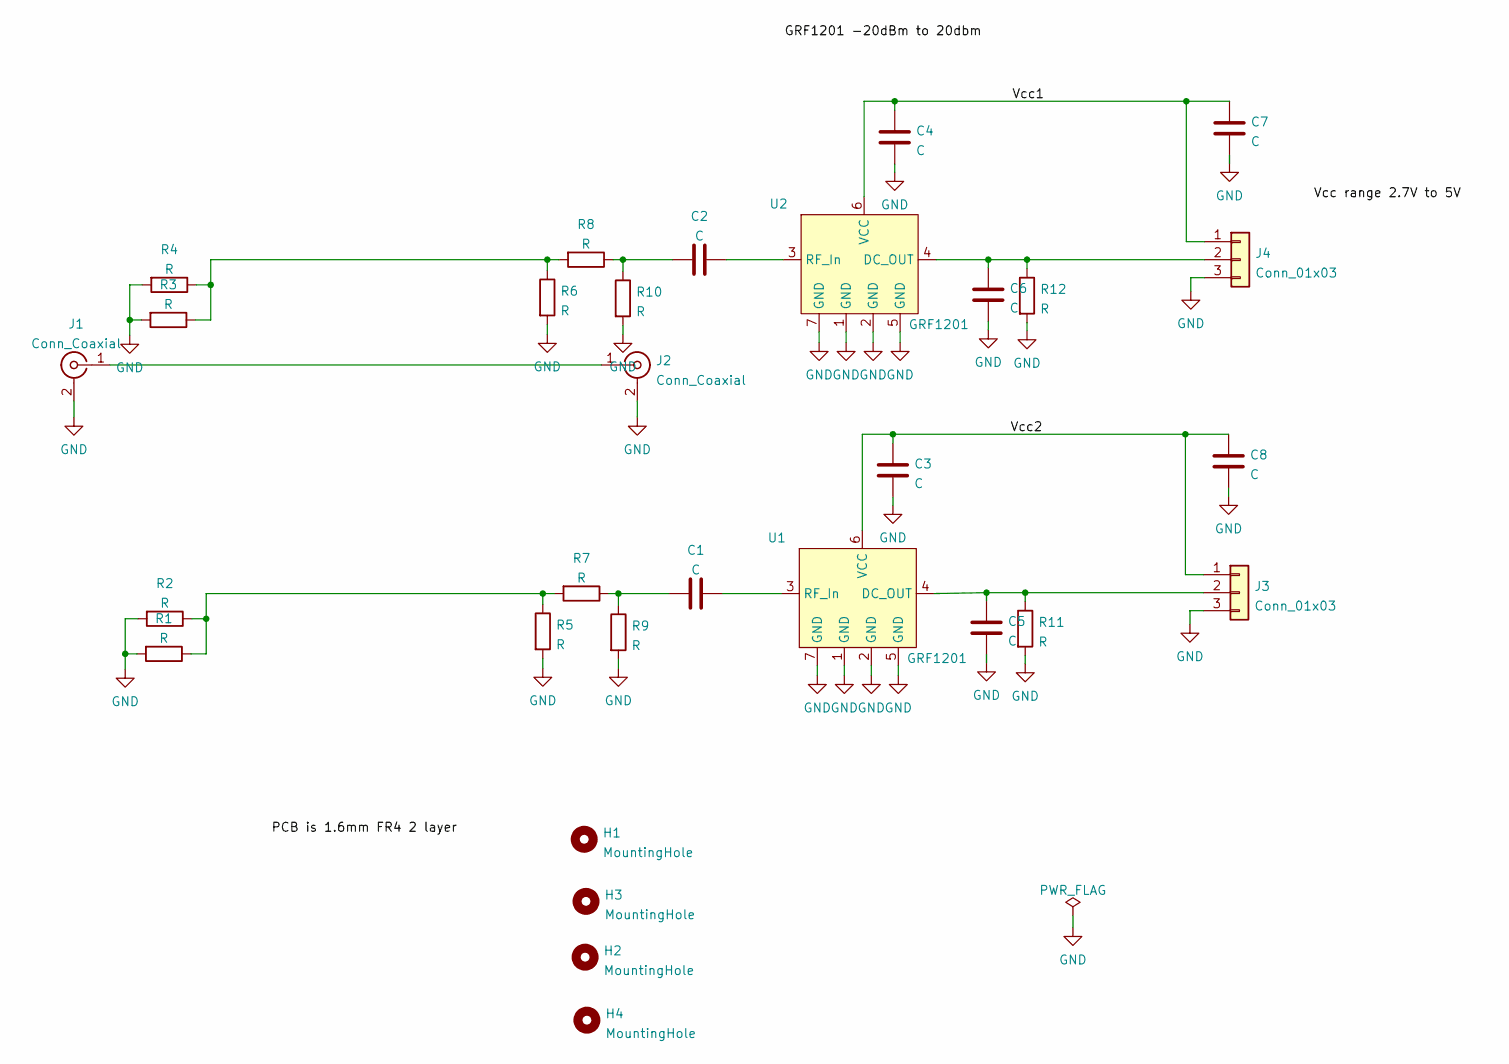
[picture p160: schematic Coupler.kicad_sch]

Parts:
C1, C2, C3, C4, C5, C6, C7, C8: C; C_0603_1608Metric
H1, H2, H3, H4: MountingHole; MountingHole_2.2mm_M2_DIN965
J1, J2: Conn_Coaxial; SMA_Samtec_SMA-J-P-X-ST-EM1_EdgeMount
J3, J4: Conn_01x03; JST_PH_B3B-PH-K_1x03_P2.00mm_Vertical
R1, R2, R3, R4, R5, R6, R7, R8, R9, R10, R11, R12: R; R_0603_1608Metric
U1, U2: GRF1201; DFN-6-1EP_1.5x1.5mm_P0.5mm_EP0.6x1..1mm

Connections:
/Vcc1: C4.1, C7.1, J4.1, U2.6 (VCC)
/Vcc2: C3.1, C8.1, J3.1, U1.6 (VCC)
GND: C3.2, C4.2, C5.2, C6.2, C7.2, C8.2, J1.2 (Ext), J2.2 (Ext), J3.3, J4.3, R1.2, R2.2, R3.2, R4.2, R5.2, R6.2, R9.2, R10.2, R11.2, R12.2, U1.1 (GND), U1.2 (GND), U1.5 (GND), U1.7 (GND), U2.1 (GND), U2.2 (GND), U2.5 (GND), U2.7 (GND)
unnamed: C1.1, R7.1, R9.1
unnamed: C1.2, U1.3 (RF_In)
unnamed: C2.1, R8.1, R10.1
unnamed: C2.2, U2.3 (RF_In)
unnamed: C5.1, J3.2, R11.1, U1.4 (DC_OUT)
unnamed: C6.1, J4.2, R12.1, U2.4 (DC_OUT)
unnamed: J1.1 (In), J2.1 (In)
unnamed: R1.1, R2.1, R5.1, R7.2
unnamed: R3.1, R4.1, R6.1, R8.2

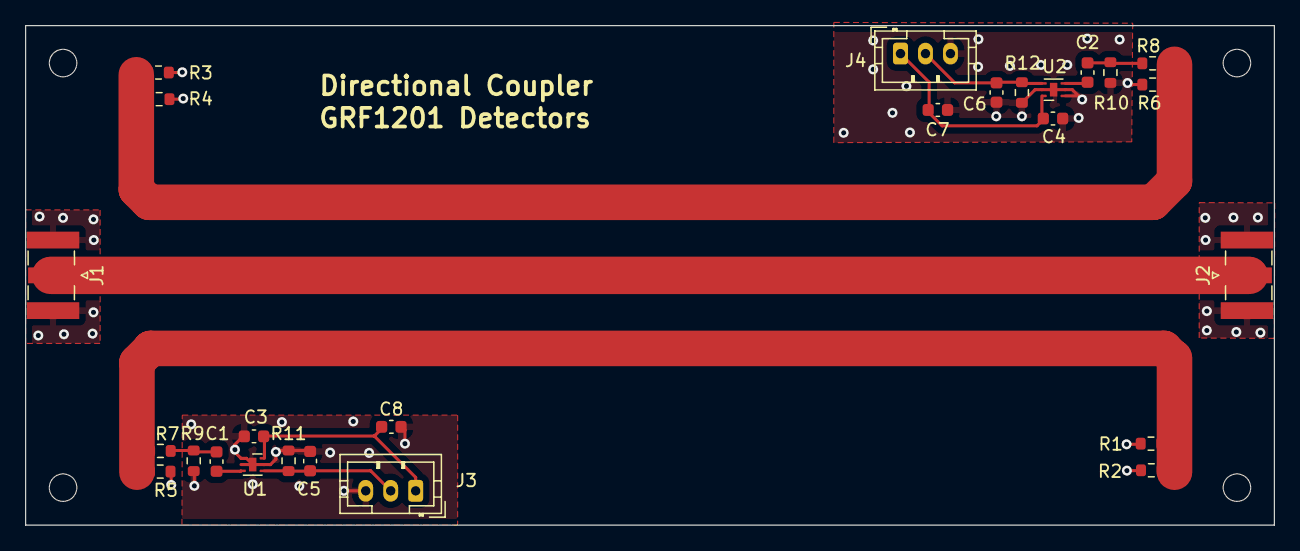
[picture p161: board Coupler.kicad_pcb from above]

Board: 2 copper layers, 100.0 x 40.0 mm, 30 parts (0 on the bottom side), 12 nets.
