M0LTE/pi-transceiver/electronics/PSU Board/pi-tranceiver-psu/pi-tranceiver-psu.kicad_pcb

## KiCad design electronics/PSU Board/pi-tranceiver-psu/pi-tranceiver-psu.kicad_pcb (2022-01-18)

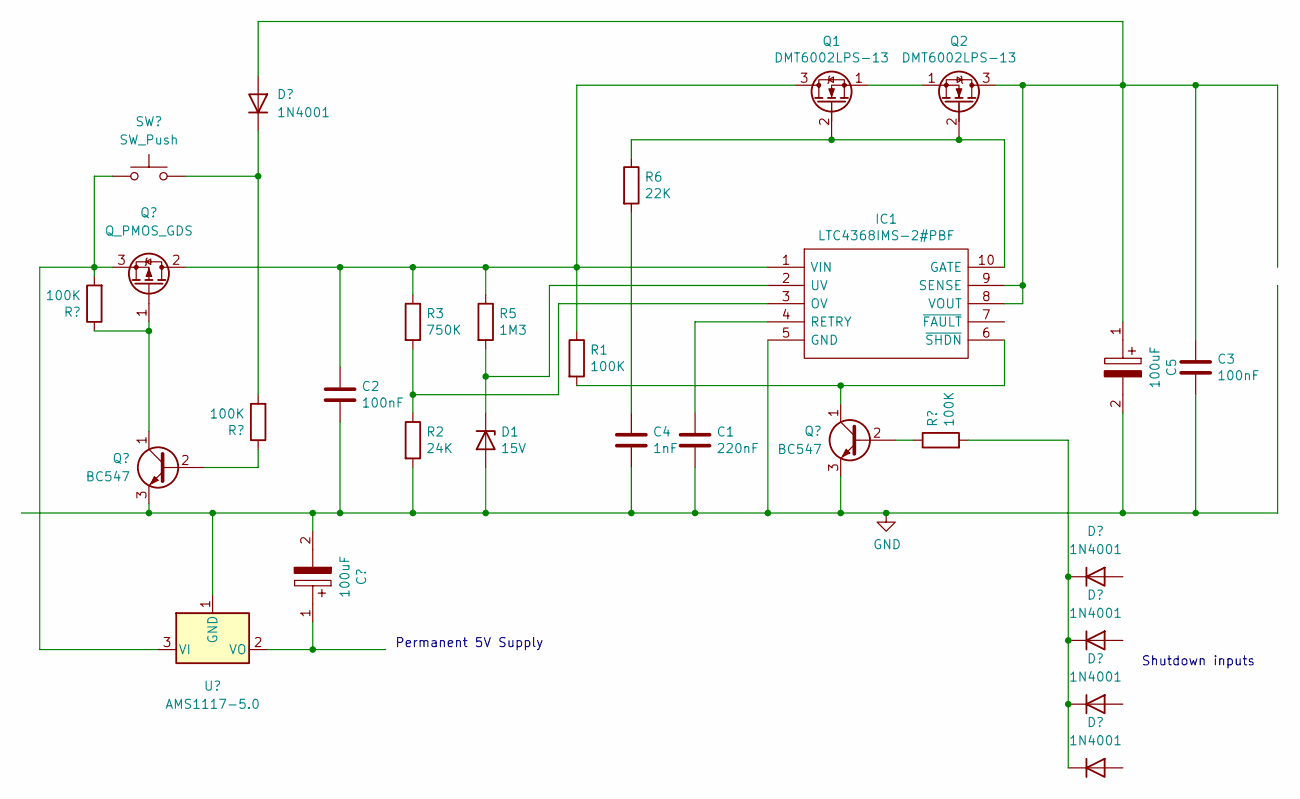
[picture p162: schematic pi-tranceiver-psu.kicad_sch]

Parts:
C1: 220nF; C_0805_2012Metric_Pad1.18x1.45mm_HandSolder
C2, C3: 100nF; C_1206_3216Metric_Pad1.33x1.80mm_HandSolder
C4: 1nF; C_0805_2012Metric_Pad1.18x1.45mm_HandSolder
C5: 100uF; CAPAE660X770N; Mouser Part Number 710-865080545012
D1: 15V; D_0805_2012Metric
IC1: LTC4368IMS-2#PBF; SOP50P490X110-10N; Mouser Part Number 584-LTC4368IMS2PBF
Q1, Q2: DMT6002LPS-13; PowerDI5060-8
R1: 100K; R_0805_2012Metric_Pad1.20x1.40mm_HandSolder
R2: 24K; R_0805_2012Metric_Pad1.20x1.40mm_HandSolder
R3: 750K; R_0805_2012Metric_Pad1.20x1.40mm_HandSolder
R5: 1M3; R_0805_2012Metric_Pad1.20x1.40mm_HandSolder
R6: 22K; R_0805_2012Metric_Pad1.20x1.40mm_HandSolder

Connections:
GND: C1.2, C2.2, C3.2, C4.2, C5.2, D1.2 (A), IC1.5 (GND), R2.2; also elsewhere on the board
unnamed: C1.1, IC1.4 (RETRY)
unnamed 2: C2.1, IC1.1 (VIN), Q1.3 (D), R1.1, R3.1, R5.1; also elsewhere on the board
unnamed 3: C3.1, C5.1, IC1.8 (VOUT), IC1.9 (SENSE), Q2.3 (D); also elsewhere on the board
unnamed: C4.1, R6.2
unnamed: D1.1 (K), IC1.2 (UV), R5.2
unnamed: IC1.3 (OV), R2.1, R3.2
unnamed: IC1.6 (~SHDN), R1.2
unnamed: IC1.10 (GATE), Q1.2 (G), Q2.2 (G), R6.1
unnamed: Q1.1 (S), Q2.1 (S)

Notes on the sheet:
Shutdown inputs
Permanent 5V Supply

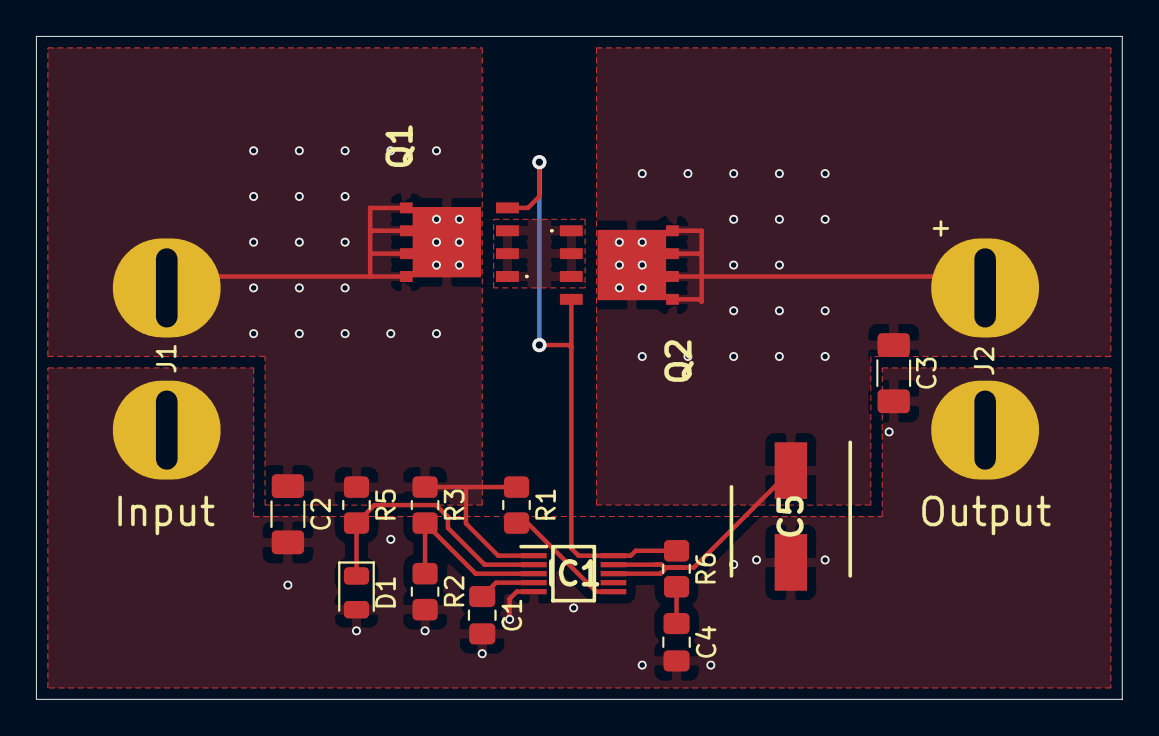
[picture p163: board pi-tranceiver-psu.kicad_pcb from above]

Board: 2 copper layers, 60.3 x 36.8 mm, 16 parts (0 on the bottom side), 10 nets.

Other parts of the board:
J1, J2: Anderson_Powerpole_2w; Anderson_powerpole_2w_90

Their connections:
GND: J1.2, J2.2; also elsewhere on the board
unnamed 2: J1.1; also elsewhere on the board
unnamed 3: J2.1; also elsewhere on the board
