M0LTE/pi-transceiver/electronics/PA_Board_V2/Arduino/Tests/Temperature/Temperature.ino

/*
Test for RADARC Pi Transceiver PA Board LM75B temperature sensor, and display it
in Celcius every 250ms. 
*/

#include <Temperature_LM75_Derived.h>

// The Generic_LM75 class will provide 12-bit temperature

Generic_LM75_12Bit temperature(&Wire);

void setup() {
  while(!Serial) {}
  
  Serial.begin(9600);

}

void loop() {
  Serial.print("Temperature = ");
  Serial.print(temperature.readTemperatureC(),1);
  Serial.println(" C");

  delay(250);
}
